alejomancinelli/FCEIA_ProyectoFinal/BL0940_ESP8266/data/collapse_button.png

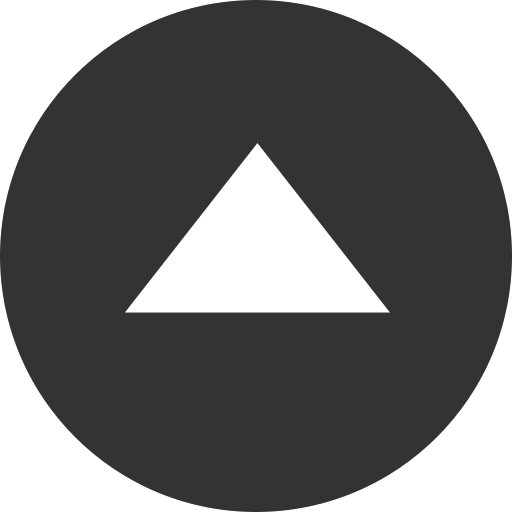
BL0940_ESP8266/data/collapse_button.png
