alejomancinelli/FCEIA_ProyectoFinal/BL0940_ESP8266/data/expand_button.png

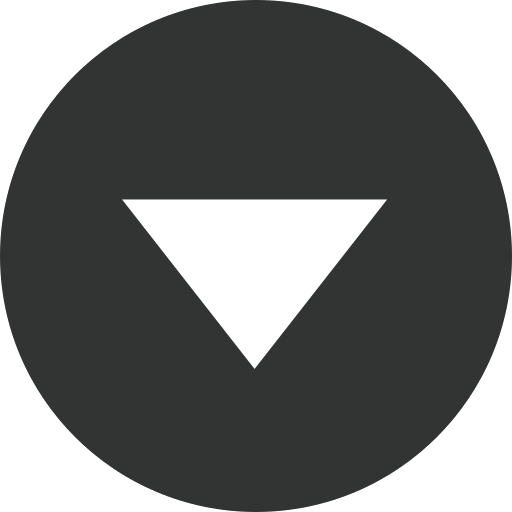
BL0940_ESP8266/data/expand_button.png
